datenhahn/cosilino-device/doc/arduino_ide_plugins/Selection_300.png

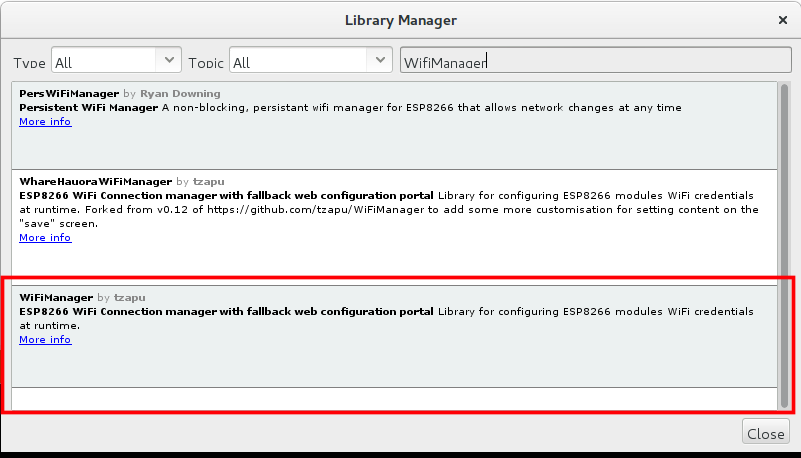
doc/arduino_ide_plugins/Selection_300.png
