datenhahn/cosilino-device/doc/images/servo_1.jpg

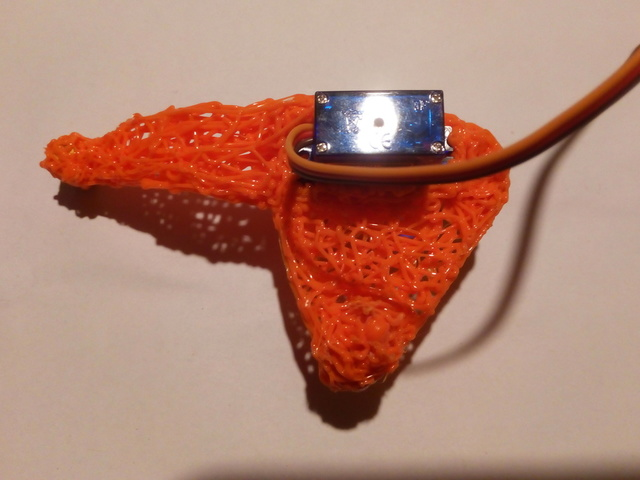
doc/images/servo_1.jpg
